crycode-de/attiny85-radiohead-dht22-weather-sensor/dht22.h

/* struct dht22 AVR Lirary
 *
 * Copyright (C) 2015 Sergey Denisov.
 * Written by Sergey Denisov aka LittleBuster (DenisovS21@gmail.com)
 *
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
 * Original library written by Adafruit Industries. MIT license.
 * 
 * https://github.com/LittleBuster/avr-dht22
 */

#ifndef __DHT22_H__
#define __DHT22_H__

#include <stdint.h>

/*
 * Sensor's port
 */
#define DDR_DHT DDRB
#define PORT_DHT PORTB
#define PIN_DHT PINB


struct dht22 {
    uint8_t data[6];    /* data from sensor store here */
    uint8_t pin;        /* DDR & PORT pin */
};

/**
 * Init dht sensor
 * @dht: sensor struct
 * @pin: PORT & DDR pin
 */
void dht_init(struct dht22 *dht, uint8_t pin);

/**
 * Reading temperature from sensor
 * @dht: sensor struct
 * @temp: out temperature pointer
 *
 * Returns 1 if succeful reading
 * Returns 0 if fail reading
 */
uint8_t dht_read_temp(struct dht22 *dht, float *temp);

/**
 * Reading humidity from sensor
 * @dht: sensor struct
 * @hum: out humidity pointer
 *
 * Returns 1 if succeful reading
 * Returns 0 if fail reading
 */
uint8_t dht_read_hum(struct dht22 *dht, float *hum);

/**
 * Reading temperature and humidity from sensor
 * @dht: sensor struct
 * @temp: out temperature pointer
 * @hum: out humidity pointer
 *
 * Returns 1 if succeful reading
 * Returns 0 if fail reading
 *
 * The fastest function for getting temperature + humidity.
 */
uint8_t dht_read_data(struct dht22 *dht, float *temp, float *hum);


#endif
